davyd-kasperovych-pustovit/Alignment-Markers-on-SiO2-Si/Batches/Batch 4/20250902_173715.jpg

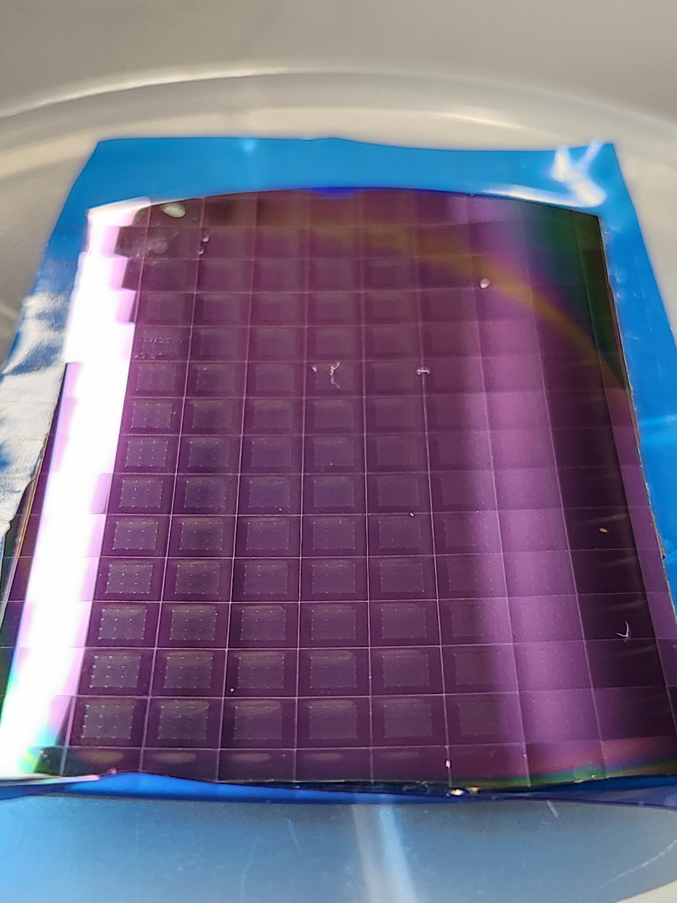
Batches/Batch 4/20250902_173715.jpg
