davyd-kasperovych-pustovit/Alignment-Markers-on-SiO2-Si/Batches/Batch 1/Picture 1 - 2micron, normal, 1.2x45mJ.jpg.jpg

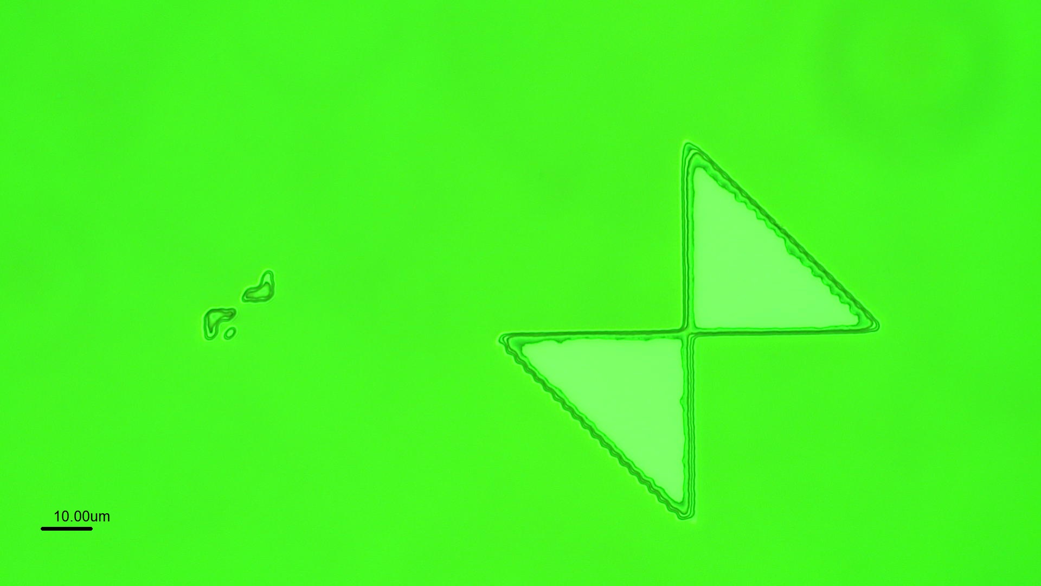
Batches/Batch 1/Picture 1 - 2micron, normal, 1.2x45mJ.jpg.jpg
