davyd-kasperovych-pustovit/Alignment-Markers-on-SiO2-Si/Batches/Batch 1/Picture 2 - 1micron, normal, 1.2x45mJ.jpg.jpg

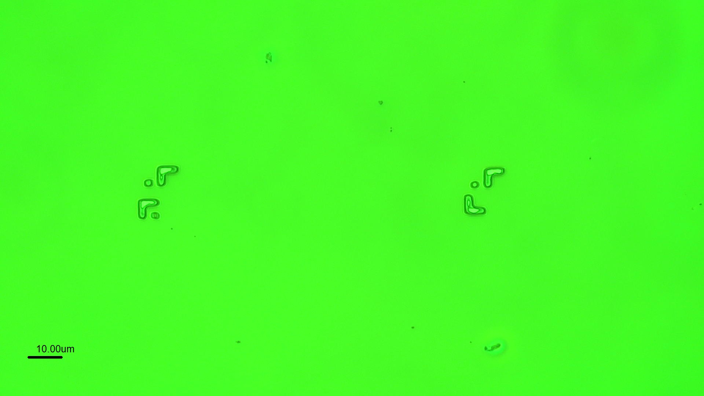
Batches/Batch 1/Picture 2 - 1micron, normal, 1.2x45mJ.jpg.jpg
