davyd-kasperovych-pustovit/Alignment-Markers-on-SiO2-Si/Batches/Batch 2/0.6um, 0.95x60mJ, Normal - 1.jpg

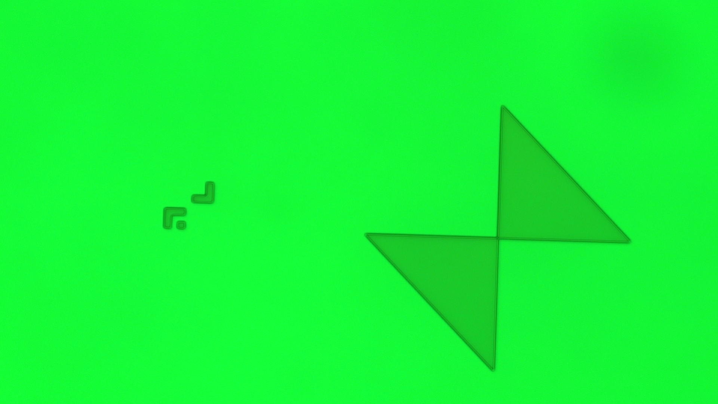
Batches/Batch 2/0.6um, 0.95x60mJ, Normal - 1.jpg
