davyd-kasperovych-pustovit/Alignment-Markers-on-SiO2-Si/Batches/Batch 2/0.6um, 1.05x60mJ, Normal.jpg

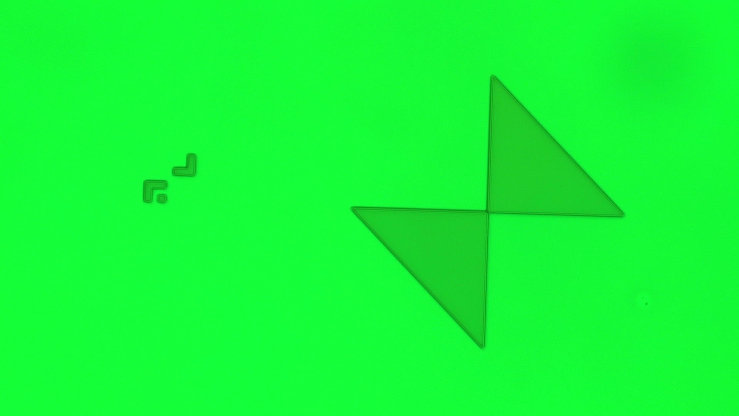
Batches/Batch 2/0.6um, 1.05x60mJ, Normal.jpg
