davyd-kasperovych-pustovit/Alignment-Markers-on-SiO2-Si/Batches/Batch 2/Picture 1 - Annotated - 1micron, normal, 1.2x60mJ.jpg.jpg

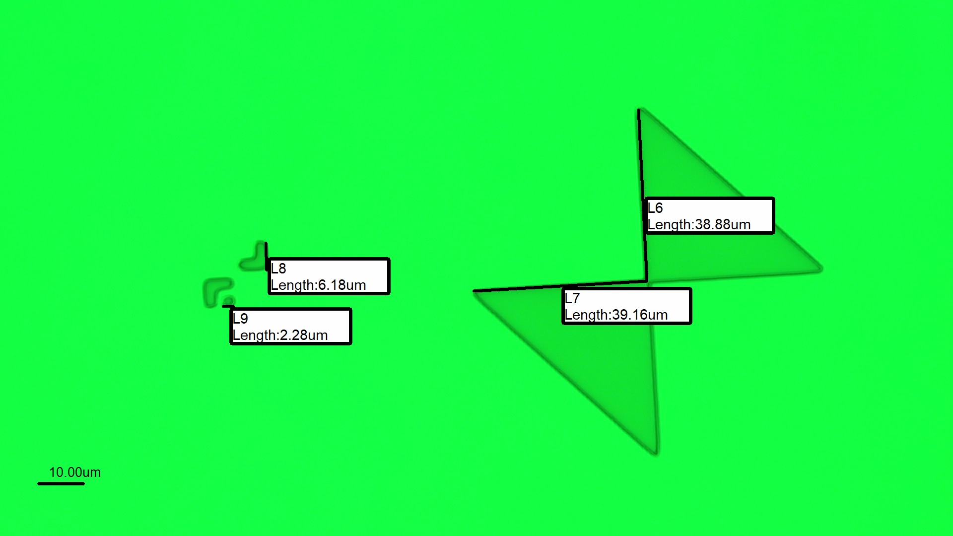
Batches/Batch 2/Picture 1 - Annotated - 1micron, normal, 1.2x60mJ.jpg.jpg
