davyd-kasperovych-pustovit/Alignment-Markers-on-SiO2-Si/Batches/Batch 3/debris and layers.jpg

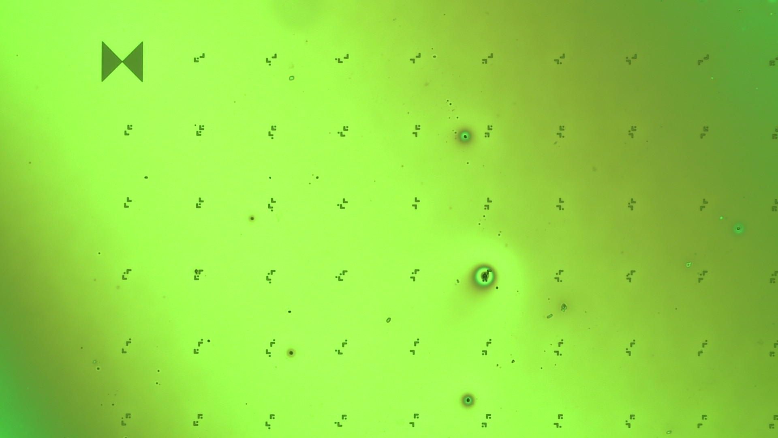
Batches/Batch 3/debris and layers.jpg
