davyd-kasperovych-pustovit/Alignment-Markers-on-SiO2-Si/Batches/Batch 3/debris_3.jpg

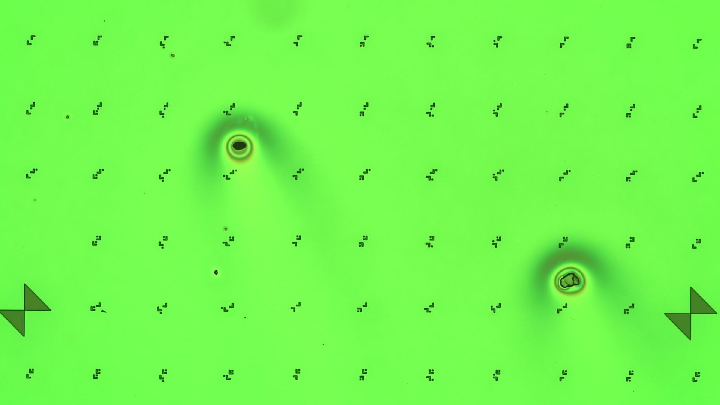
Batches/Batch 3/debris_3.jpg
