davyd-kasperovych-pustovit/Alignment-Markers-on-SiO2-Si/Batches/Batch 3/recipie photo_1.jpg

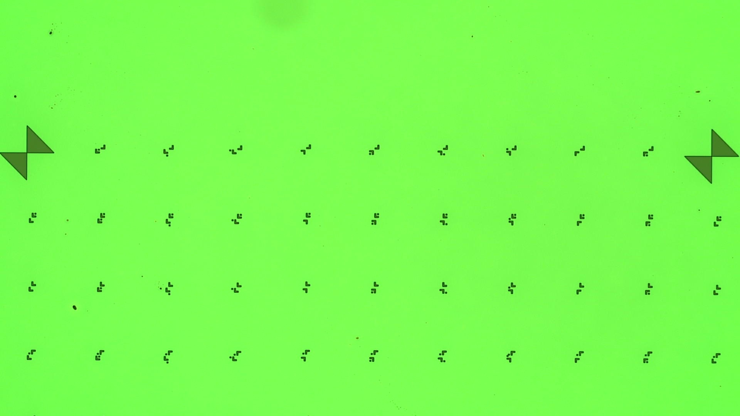
Batches/Batch 3/recipie photo_1.jpg
