davyd-kasperovych-pustovit/Alignment-Markers-on-SiO2-Si/Batches/Batch 4/Expected_Quality_After_Metal_Deposition_1.jpg

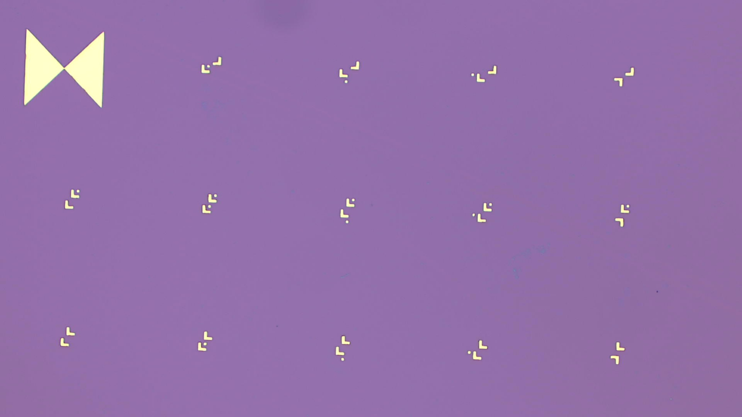
Batches/Batch 4/Expected_Quality_After_Metal_Deposition_1.jpg
