davyd-kasperovych-pustovit/Alignment-Markers-on-SiO2-Si/Lift Off Testing/With Ultrasonic/development_6.jpg

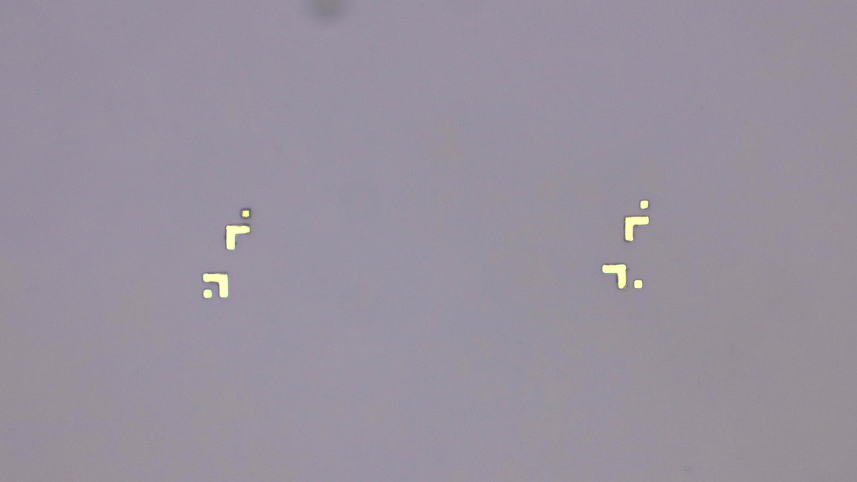
Lift Off Testing/With Ultrasonic/development_6.jpg
