davyd-kasperovych-pustovit/Alignment-Markers-on-SiO2-Si/Lift Off Testing/Without Ultrasonic/Lift Off - 3.jpg

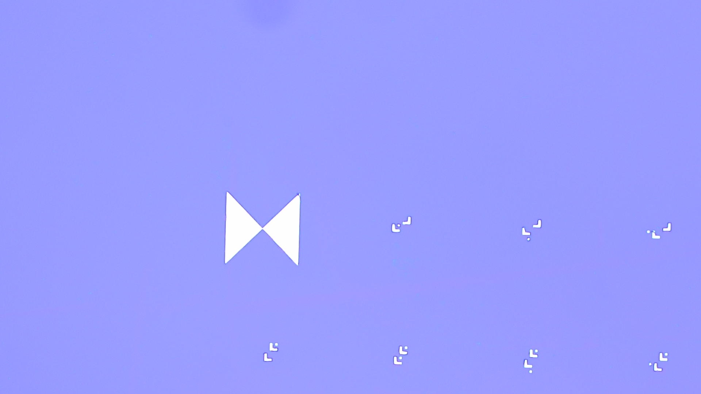
Lift Off Testing/Without Ultrasonic/Lift Off - 3.jpg
